Svetoscope/Walk-Man/Walkman_CAD/LEGS/QUADRICEP.SLDPRT

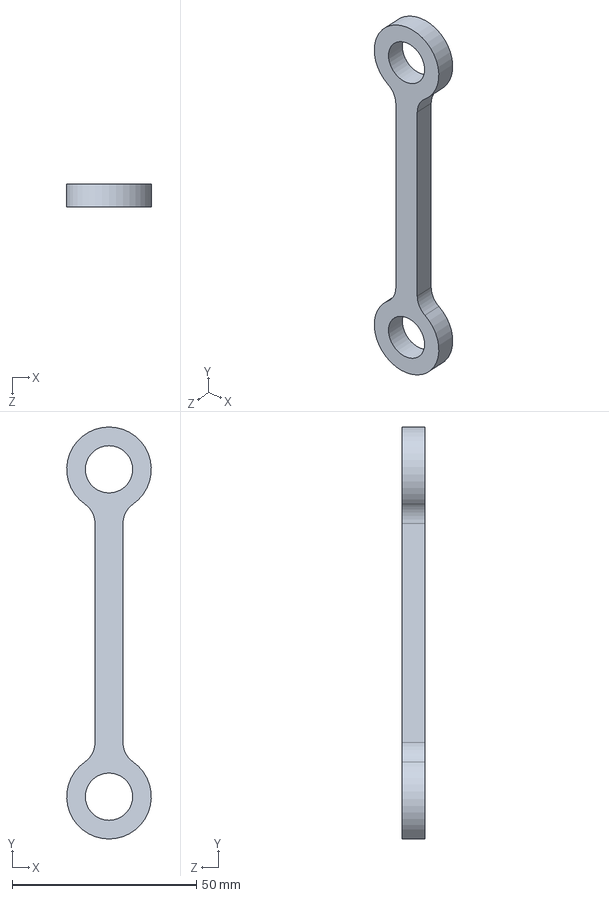
[picture p11: CAD file, 2024-04-14]
Walkman_CAD/LEGS/QUADRICEP.SLDPRT
23.0 x 111.9 x 6.35 mm
