Svetoscope/Walk-Man/Walkman_CAD/PELVIS/Stainless Steel Ball Bearing.SLDPRT

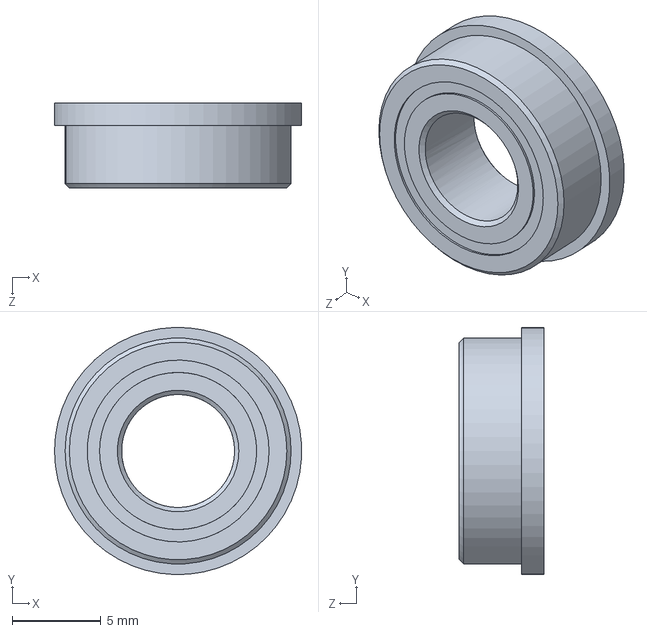
[picture p12: CAD file, 2024-04-14]
Walkman_CAD/PELVIS/Stainless Steel Ball Bearing.SLDPRT
13.9 x 13.9 x 4.76 mm
