Svetoscope/Walk-Man/Walkman_CAD/LEGS/KNEECAP.SLDPRT

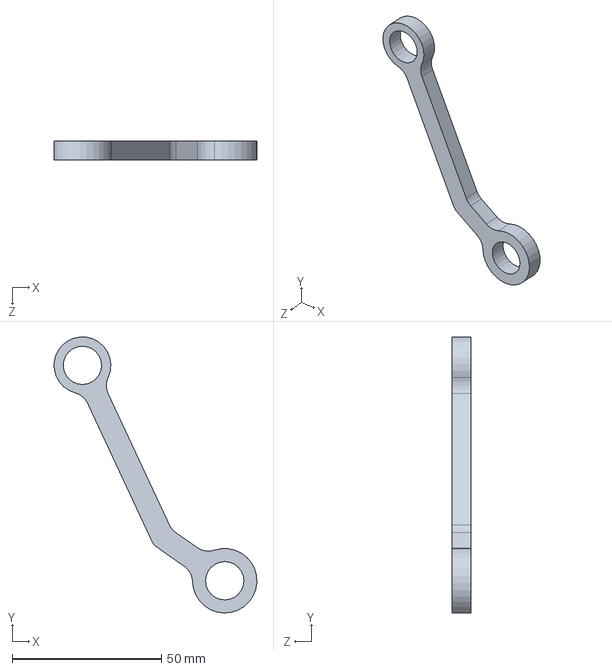
[picture p13: CAD file, 2024-04-14]
Walkman_CAD/LEGS/KNEECAP.SLDPRT
67.9 x 92.4 x 6.35 mm
