Svetoscope/Walk-Man/Walkman_CAD/PELVIS/Standoff.SLDPRT

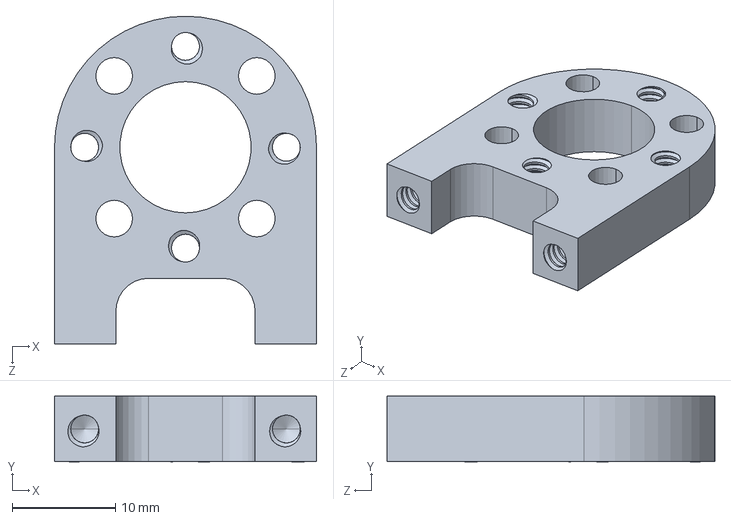
[picture p14: CAD file, 2024-04-14]
Walkman_CAD/PELVIS/Standoff.SLDPRT
25.4 x 6.35 x 31.8 mm
