Svetoscope/Walk-Man/Walkman_CAD/WAIST/Switch.SLDPRT

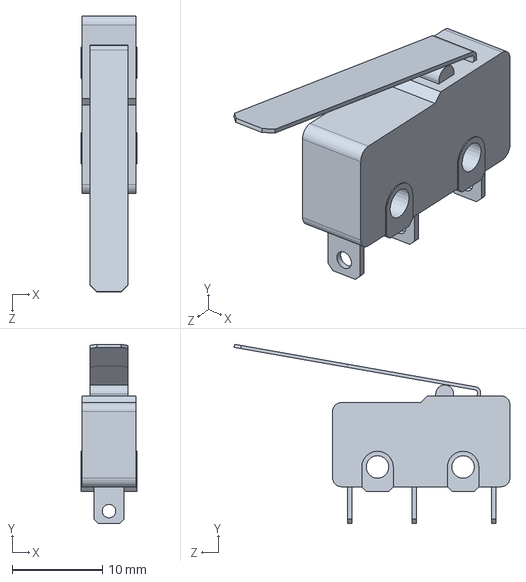
[picture p15: CAD file, 2024-04-14]
Walkman_CAD/WAIST/Switch.SLDPRT
6.20 x 19.9 x 30.6 mm
