Svetoscope/Walk-Man/Walkman_CAD/LEGS/D-Profile Rotary Shaft 2in.SLDPRT

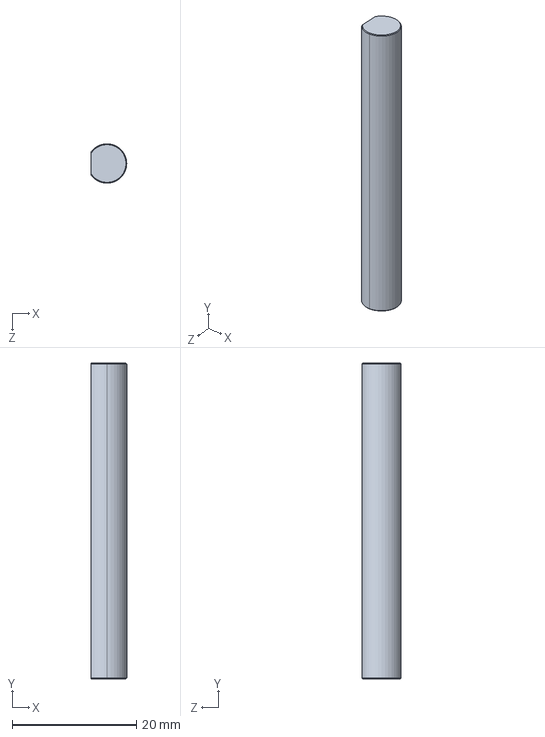
[picture p16: CAD file, 2024-04-14]
Walkman_CAD/LEGS/D-Profile Rotary Shaft 2in.SLDPRT
5.72 x 50.8 x 6.34 mm
