Svetoscope/Walk-Man/Walkman_CAD/PELVIS/PELVIS.SLDPRT

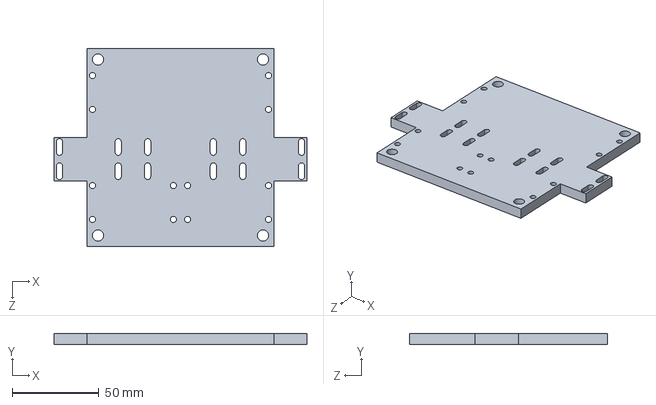
[picture p17: CAD file, 2024-04-14]
Walkman_CAD/PELVIS/PELVIS.SLDPRT
146.1 x 6.35 x 114.3 mm
