Svetoscope/Walk-Man/Walkman_CAD/WAIST/WAIST.SLDPRT

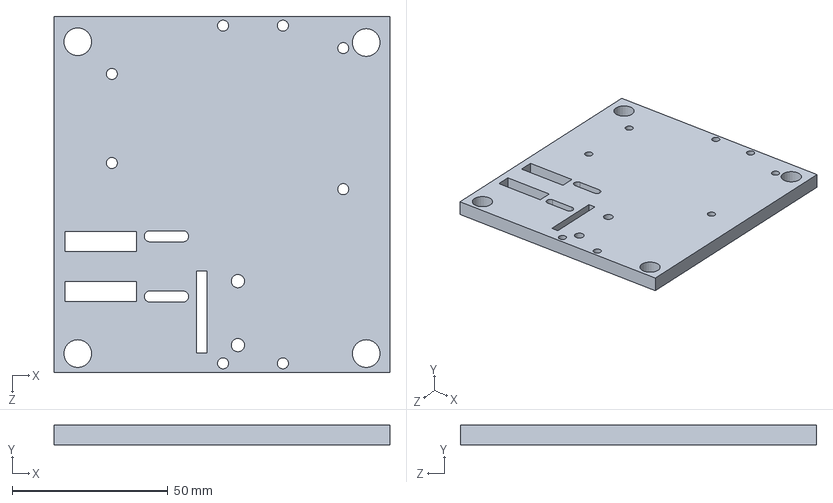
[picture p18: CAD file, 2024-04-14]
Walkman_CAD/WAIST/WAIST.SLDPRT
107.7 x 6.35 x 114.2 mm
