Svetoscope/Walk-Man/Walkman_CAD/PELVIS/ENGINE_SUPPORT_W250.SLDPRT

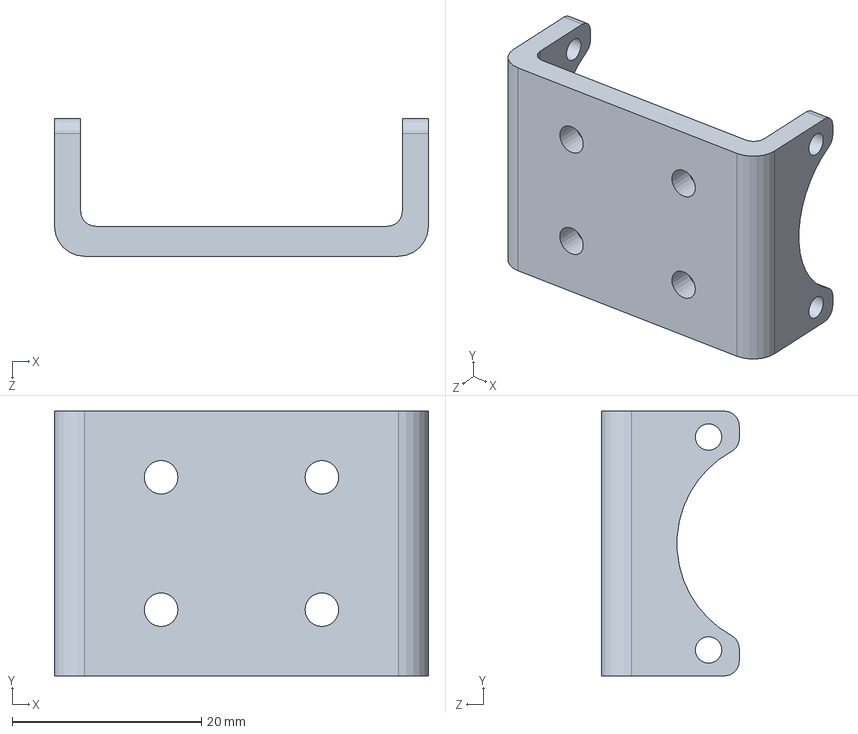
[picture p19: CAD file, 2024-04-14]
Walkman_CAD/PELVIS/ENGINE_SUPPORT_W250.SLDPRT
39.5 x 28.0 x 14.5 mm
