Svetoscope/Walk-Man/Walkman_CAD/LEGS/THIGH.SLDPRT

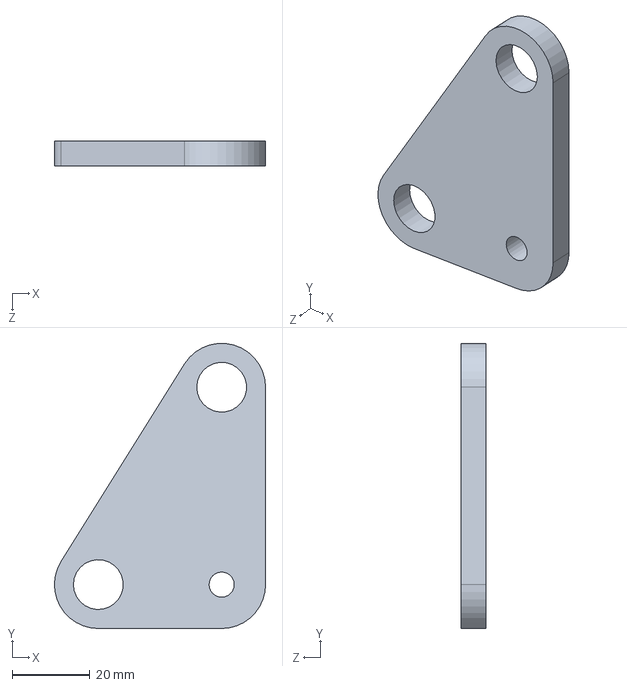
[picture p20: CAD file, 2024-04-14]
Walkman_CAD/LEGS/THIGH.SLDPRT
54.4 x 73.4 x 6.35 mm
