Svetoscope/Walk-Man/Walkman_CAD/LEGS/TIBIA.SLDPRT

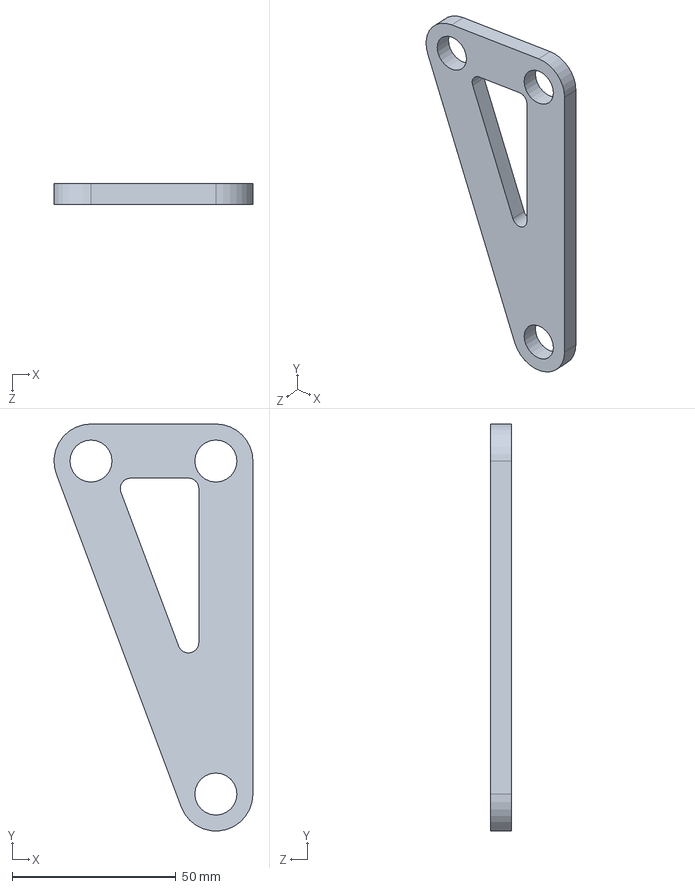
[picture p21: CAD file, 2024-04-14]
Walkman_CAD/LEGS/TIBIA.SLDPRT
60.7 x 124.2 x 6.35 mm
