Svetoscope/Walk-Man/Walkman_CAD/WAIST/ENGINE_SUPPORT_W350.SLDPRT

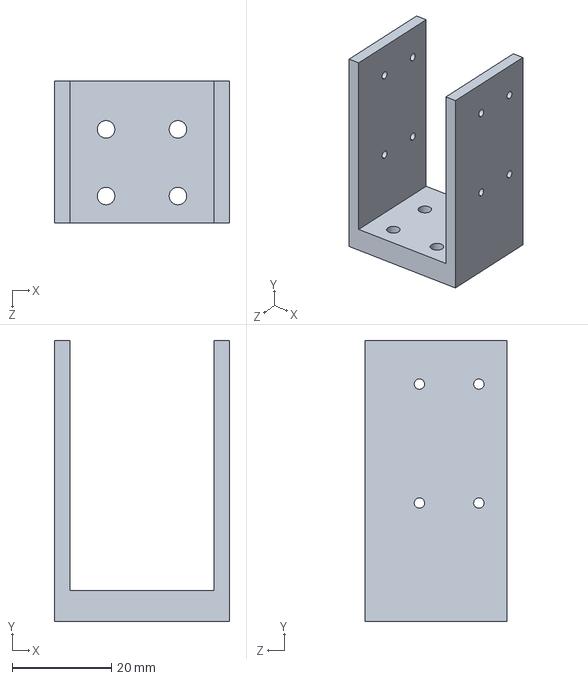
[picture p22: CAD file, 2024-04-14]
Walkman_CAD/WAIST/ENGINE_SUPPORT_W350.SLDPRT
35.3 x 56.7 x 28.7 mm
