Svetoscope/Walk-Man/Walkman_CAD/WAIST/WEIGHT.SLDPRT

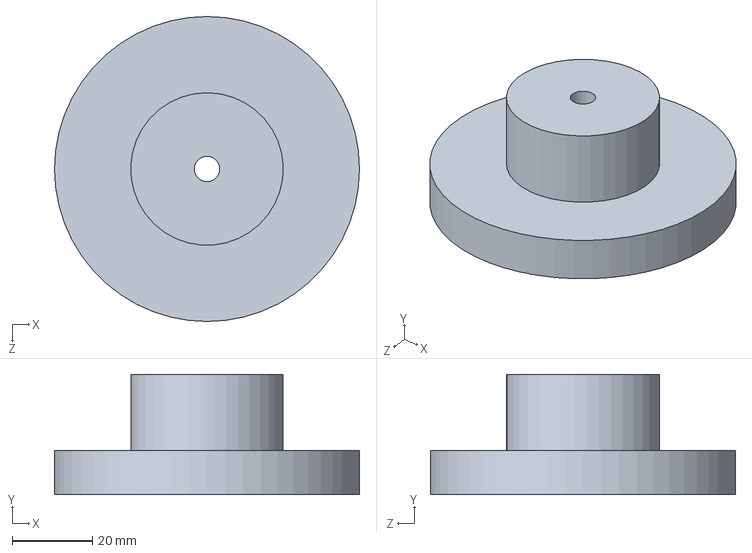
[picture p23: CAD file, 2024-04-14]
Walkman_CAD/WAIST/WEIGHT.SLDPRT
76.2 x 30.0 x 76.2 mm
