Svetoscope/Walk-Man/Walkman_CAD/WAIST/MOTOR_COUPLER_W350.SLDPRT

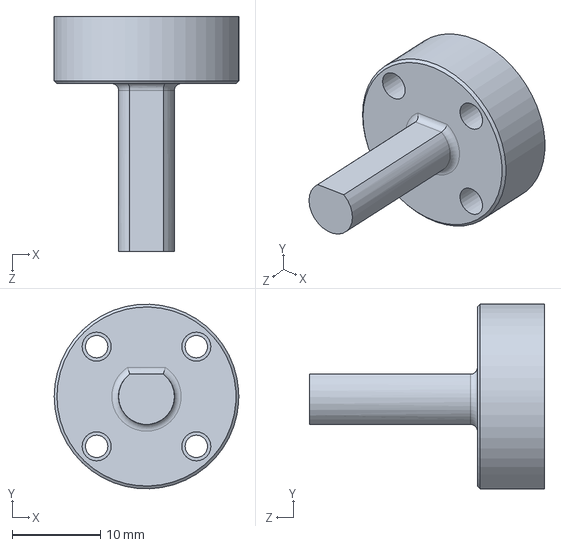
[picture p24: CAD file, 2024-04-14]
Walkman_CAD/WAIST/MOTOR_COUPLER_W350.SLDPRT
21.0 x 20.9 x 26.7 mm
