Svetoscope/Walk-Man/Walkman_CAD/PELVIS/XL430_W250_T.SLDASM

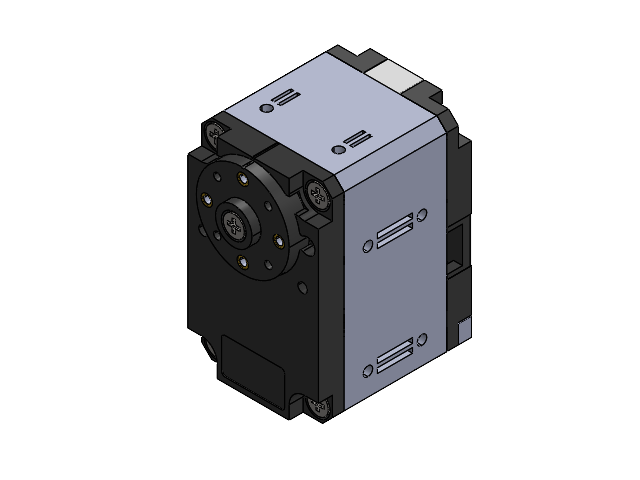
[picture p29: CAD file, 2024-04-14]
Walkman_CAD/PELVIS/XL430_W250_T.SLDASM
Part1_XL430_W250_T.STEP
Part2_XL430_W250_T.STEP
Part3_XL430_W250_T.STEP
Part4_XL430_W250_T.STEP
countersunk flat head cross recess screw_din_DIN EN ISO 7046-1 - M2.5 x 10 - Z - 10N.STEP x 9
Part5_XL430_W250_T.STEP
Part6_XL430_W250_T.STEP
