Svetoscope/Walk-Man/Walkman_CAD/WAIST/MPU-9250.SLDASM

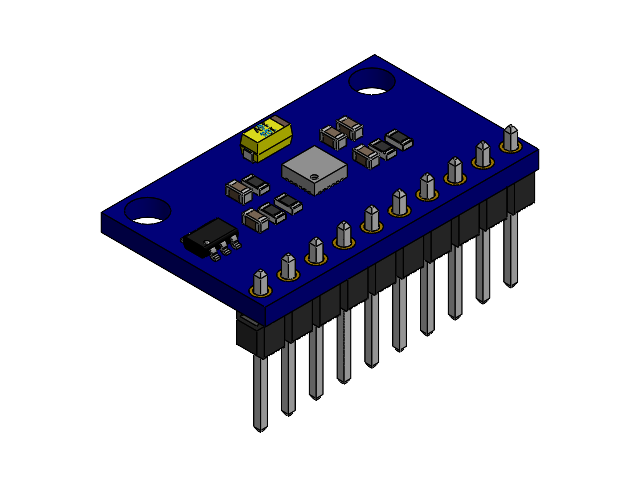
[picture p30: CAD file, 2024-04-14]
Walkman_CAD/WAIST/MPU-9250.SLDASM
board.stp
hole_plating.stp x 20
Pin Header 1x10 TH Pitch 2.54mm.stp
MPU-9250_1.stp
tantalum 10uF.stp
SOT23_5.stp
RESC-0603.stp x 5
CAPC-0603-T0.9-BN.stp x 5
